mrWheel/mqttAerosolSensor/documentation/IMG_9012.JPG

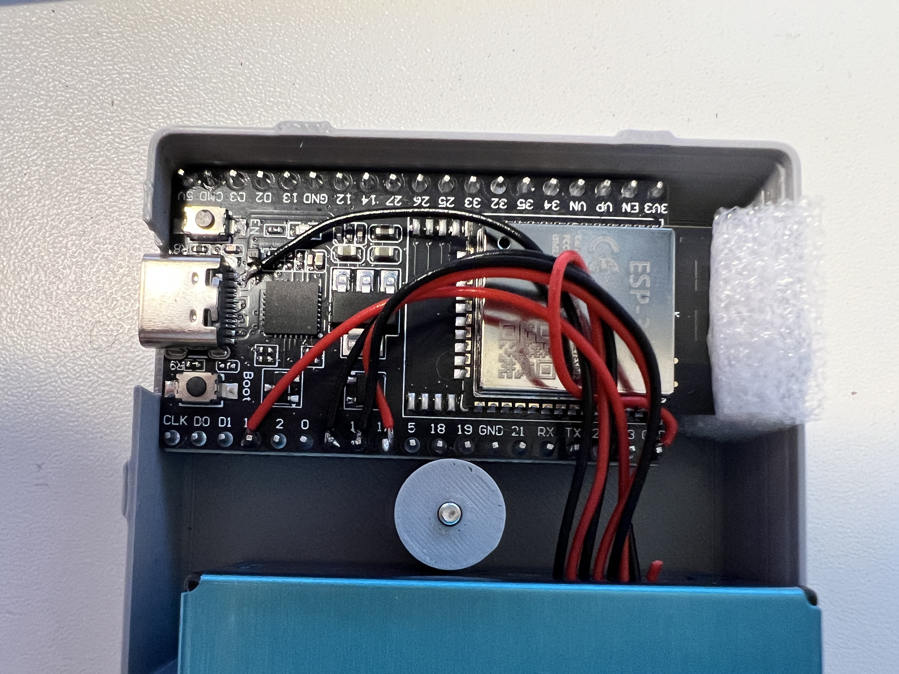
documentation/IMG_9012.JPG
