mrWheel/mqttAerosolSensor/documentation/IMG_9013.JPG

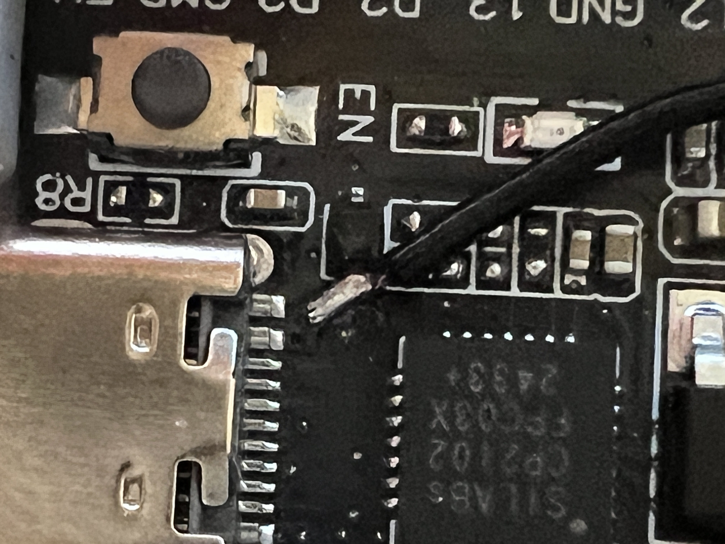
documentation/IMG_9013.JPG
