mrWheel/mqttAerosolSensor/documentation/IMG_9014.JPG

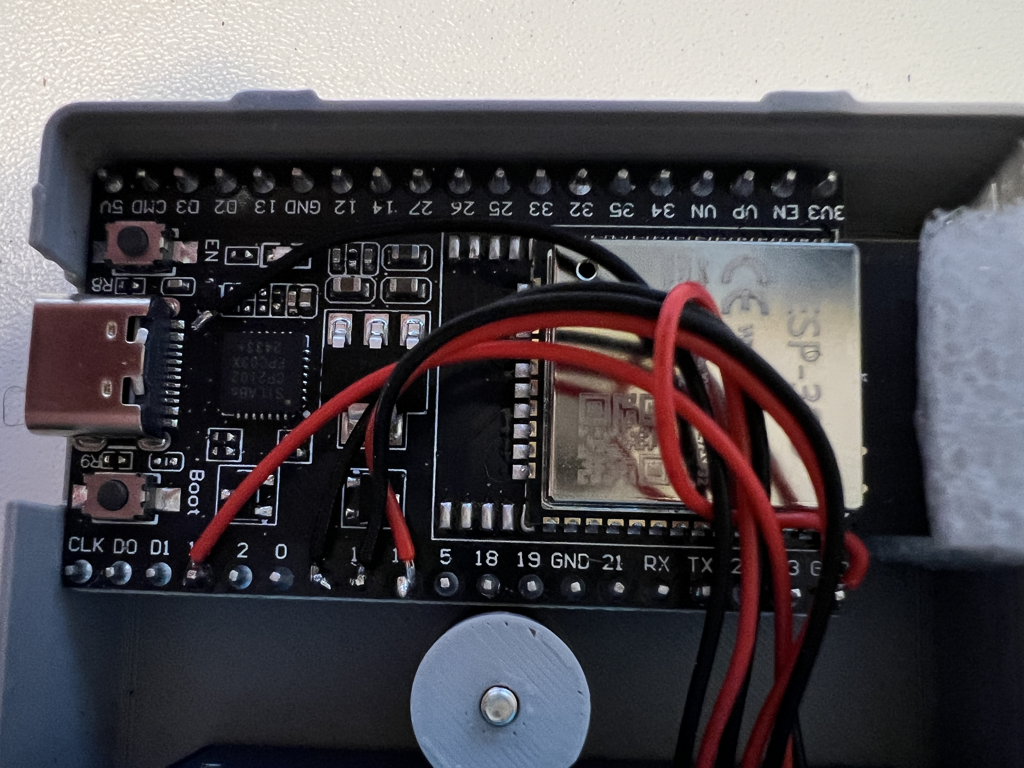
documentation/IMG_9014.JPG
