mrWheel/mqttAerosolSensor/KiCAD/mqttAerosolSensor/luchtSensor.kicad_sch

## KiCad design KiCAD/mqttAerosolSensor/luchtSensor.kicad_sch (2026-02-20)

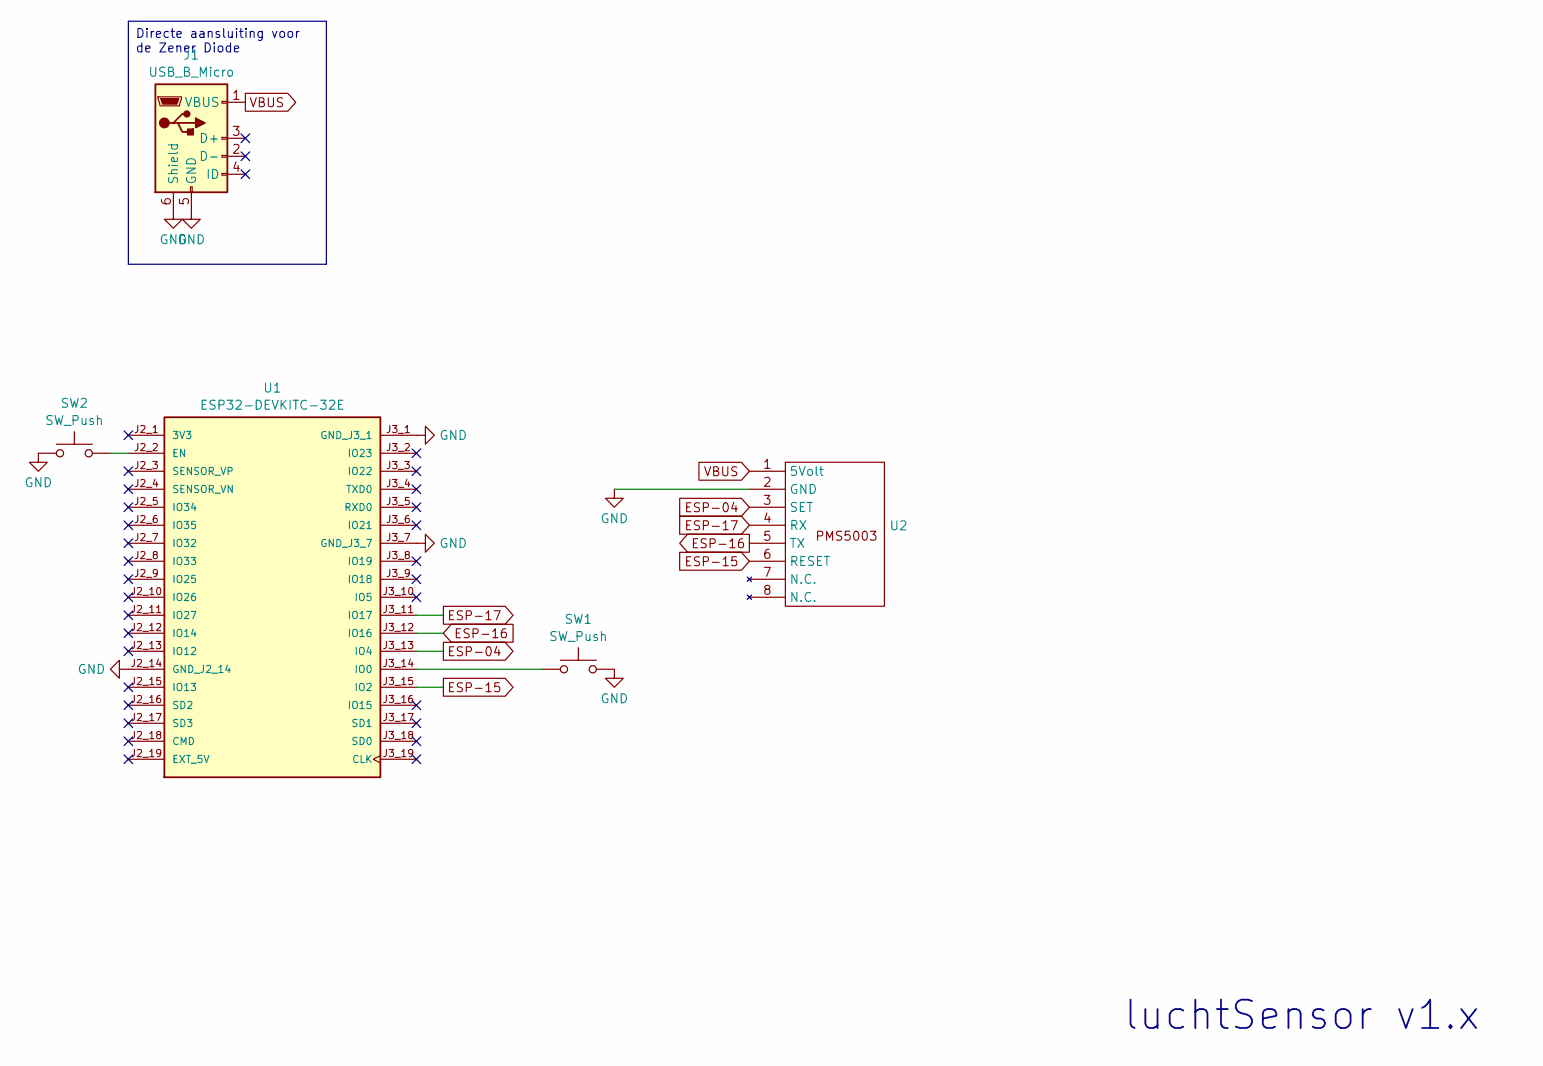
[picture p13: schematic luchtSensor.kicad_sch]

Parts:
J1: USB_B_Micro
SW1, SW2: SW_Push
U1: ESP32-DEVKITC-32E; MODULE_ESP32-DEVKITC-32E; PARTREV 1.4
U2: (no value)

Connections:
ESP-04: U1.J3_13 (IO4), U2.3 (SET)
ESP-15: U1.J3_15 (IO2), U2.6 (RESET)
ESP-16: U1.J3_12 (IO16), U2.5 (TX)
ESP-17: U1.J3_11 (IO17), U2.4 (RX)
GND: J1.5 (GND), J1.6 (Shield), SW1.2, SW2.1, U1.J2_14 (GND_J2_14), U1.J3_1 (GND_J3_1), U1.J3_7 (GND_J3_7), U2.2 (GND)
unnamed: SW1.1, U1.J3_14 (IO0)
unnamed: SW2.2, U1.J2_2 (EN)
VBUS: J1.1 (VBUS), U2.1 (5Volt)

Notes on the sheet:
luchtSensor v1.x
Directe aansluiting voor de Zener Diode
